laulin/ntronic/modules/bases/base_T_1x1.png

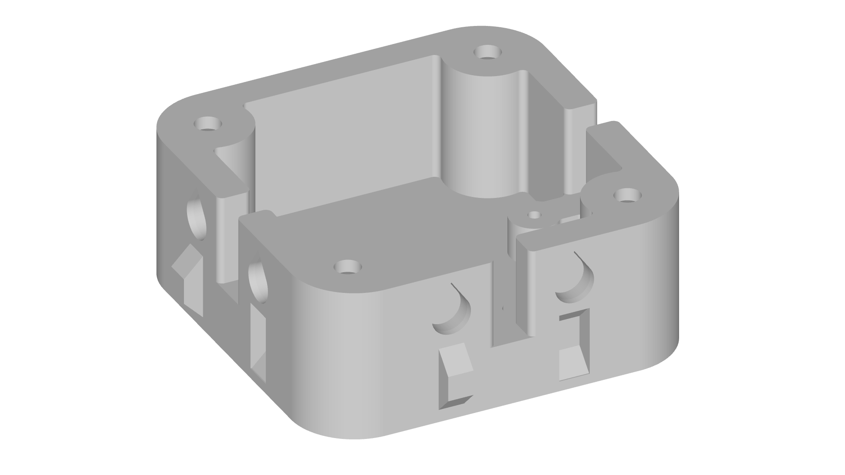
modules/bases/base_T_1x1.png
